pirathi2002/Muscle-Cramp-Detector/Cicuit/Sto2.asc

C1: cap; 1000µ
C2: cap; 1000µ
C3: cap; 100µ
C4: cap; 100µ
I1: current; SINE(0.1 0.5 1000)
I2: current; SINE(0.1 0.5 2000)
R1: res; 1000
R2: res; 1000
R3: res; 1000
R4: res; 1000
R5: res; 1000
R6: res; 1000
R7: res; 1000
R8: res; 1000
R9: res; 1000
R10: res; 1700
R11: res; 1700
R12: res; 1000
U1: LT1816
U2: LT1816
U3: LT1816
U4: LT1816
V1: voltage; 15
V2: voltage; 15
Named nets: 0
.tran 1
